ebredder/Awesome-Automata/pics/IMG_20191008_003500.jpg

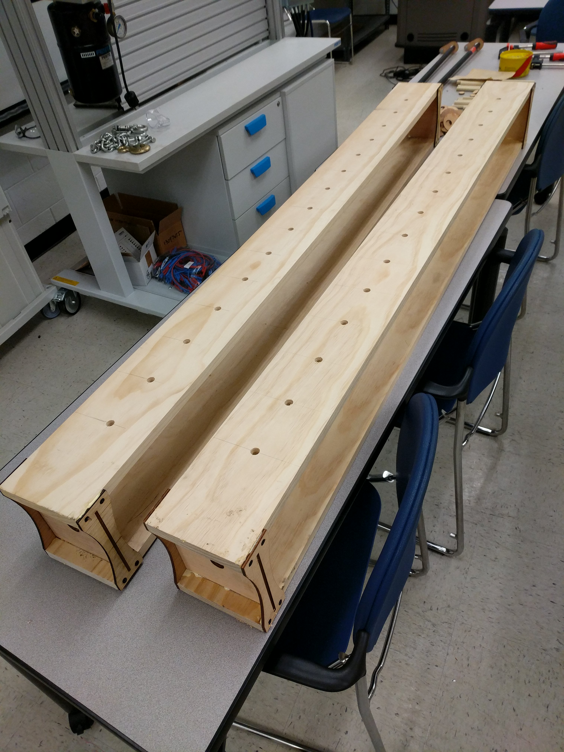
pics/IMG_20191008_003500.jpg
