ebredder/Awesome-Automata/pics/IMG_20191008_003507.jpg

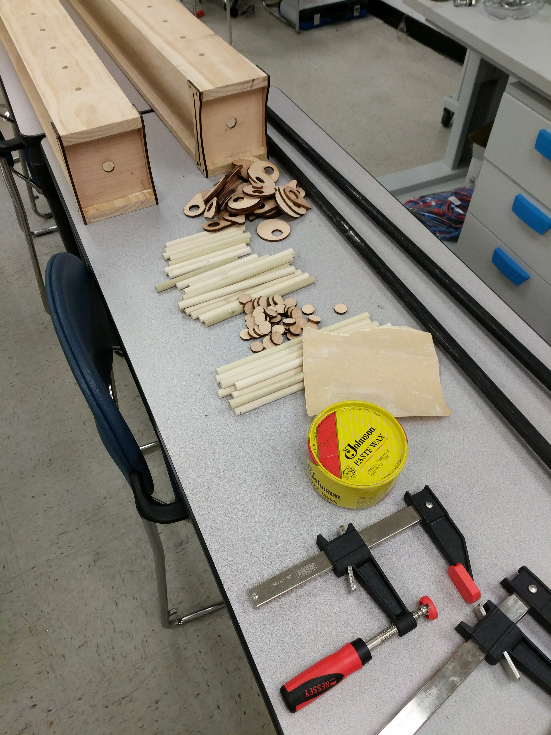
pics/IMG_20191008_003507.jpg
