ebredder/Awesome-Automata/pics/IMG_20191008_091442.jpg

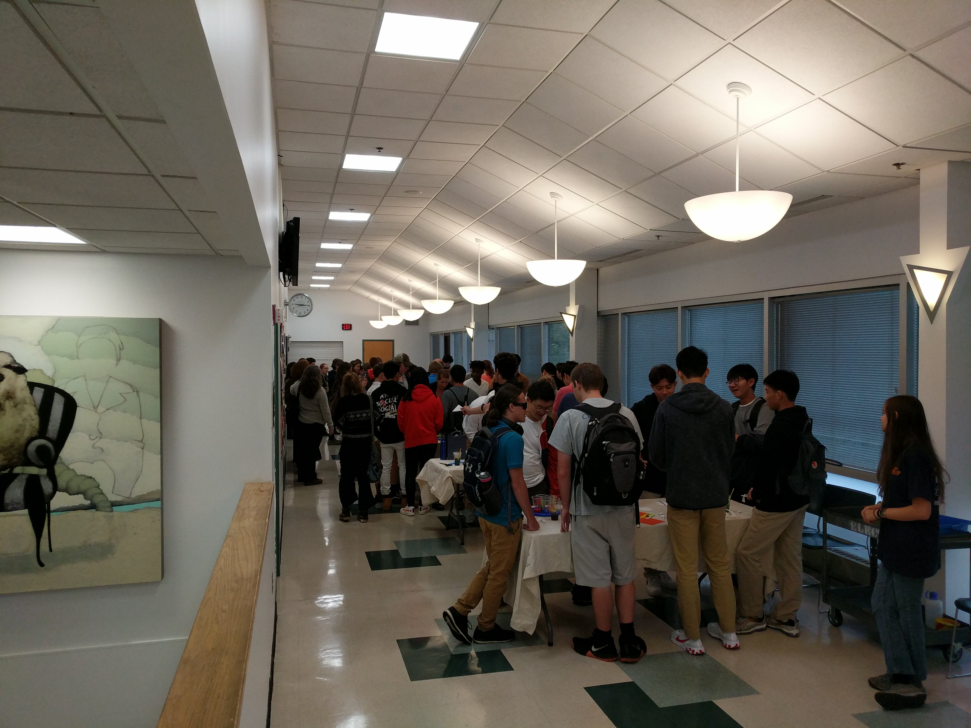
pics/IMG_20191008_091442.jpg
