ebredder/Awesome-Automata/pics/IMG_20191008_094549.jpg

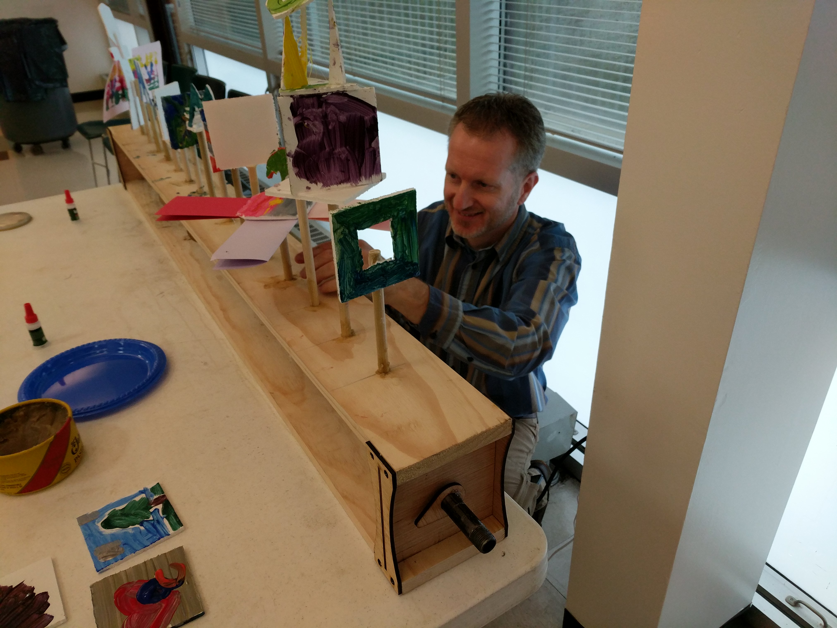
pics/IMG_20191008_094549.jpg
